hris-2/Crown_Keyboard/Ergogen/Outputs/left_stilts.dxf

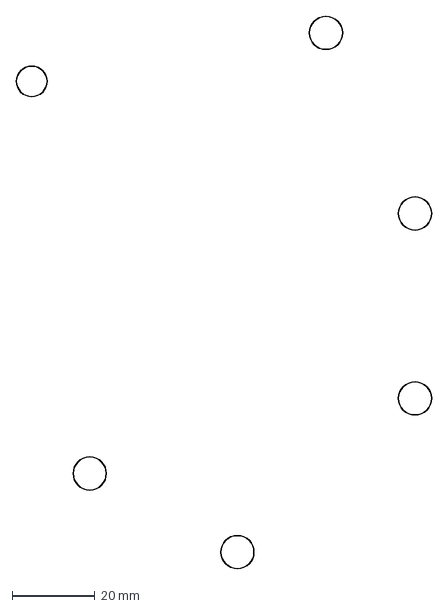
[picture p16: CAD file, 2025-05-29]
Ergogen/Outputs/left_stilts.dxf
100.2 x 133.3 mm
