hris-2/Crown_Keyboard/Ergogen/Outputs/Outlines/left_xlboard.dxf

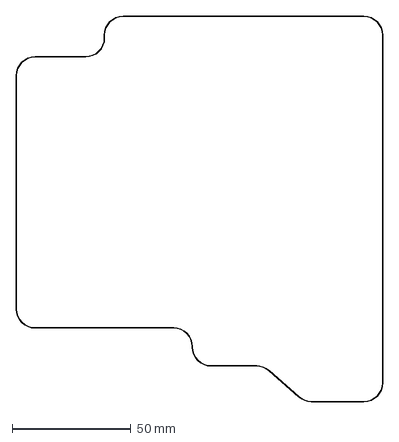
[picture p17: CAD file, 2025-05-29]
Ergogen/Outputs/Outlines/left_xlboard.dxf
154.0 x 162.0 mm
