hris-2/Crown_Keyboard/Ergogen/Outputs/left_mounting_holes.dxf

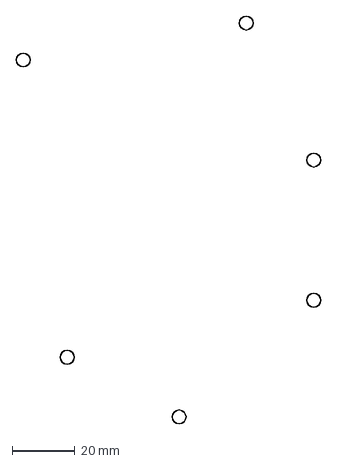
[picture p19: CAD file, 2025-05-29]
Ergogen/Outputs/left_mounting_holes.dxf
96.9 x 129.7 mm
