hris-2/Crown_Keyboard/Ergogen/Outputs/Outlines/left_niceview_template.dxf

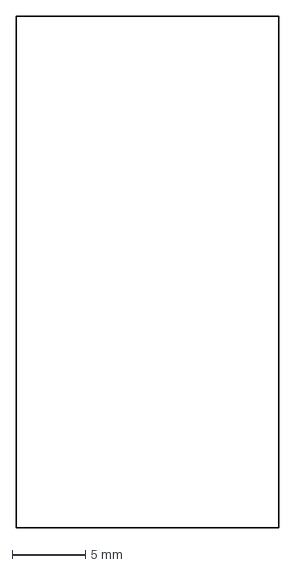
[picture p20: CAD file, 2025-05-29]
Ergogen/Outputs/Outlines/left_niceview_template.dxf
18.0 x 35.0 mm
