hris-2/Crown_Keyboard/Ergogen/Outputs/Unimportant/left_stilts-bottom_middle.dxf

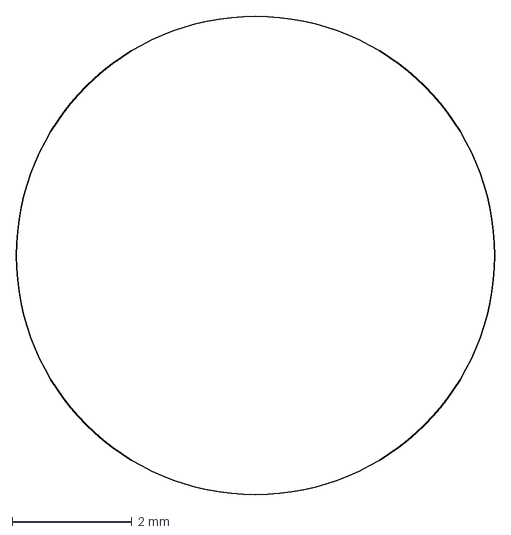
[picture p21: CAD file, 2025-05-29]
Ergogen/Outputs/Unimportant/left_stilts-bottom_middle.dxf
8.00 x 8.00 mm
