hris-2/Crown_Keyboard/Ergogen/Outputs/Outlines/left_stilts_w_holes.dxf

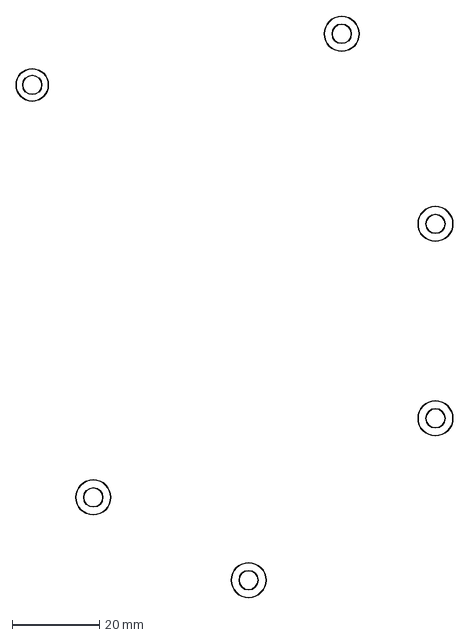
[picture p22: CAD file, 2025-05-29]
Ergogen/Outputs/Outlines/left_stilts_w_holes.dxf
100.2 x 133.3 mm
