hris-2/Crown_Keyboard/Ergogen/Outputs/right_pcb.dxf

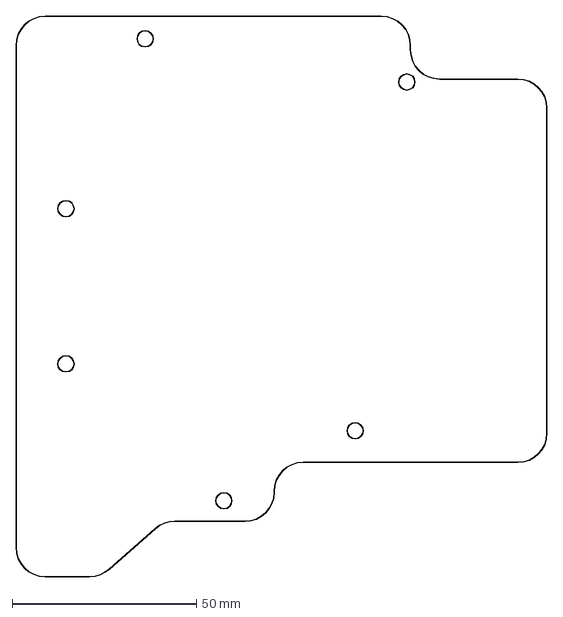
[picture p23: CAD file, 2025-05-29]
Ergogen/Outputs/right_pcb.dxf
144.0 x 152.0 mm
