hris-2/Crown_Keyboard/Ergogen/Outputs/both_combo.dxf

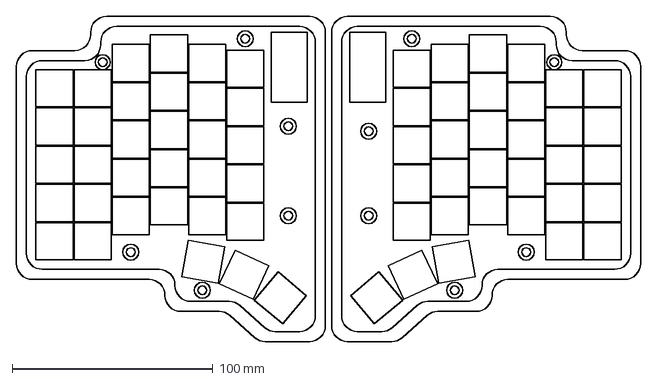
[picture p25: CAD file, 2025-05-29]
Ergogen/Outputs/both_combo.dxf
311.0 x 162.0 mm
