hris-2/Crown_Keyboard/Ergogen/Outputs/Outlines/left_stilts.dxf

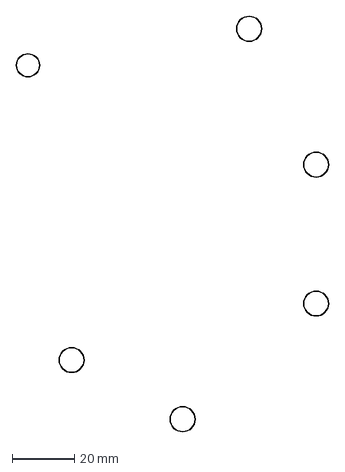
[picture p26: CAD file, 2025-05-29]
Ergogen/Outputs/Outlines/left_stilts.dxf
100.2 x 133.3 mm
