hris-2/Crown_Keyboard/Ergogen/Outputs/Unimportant/right_mounting_hole-bottom_left.dxf

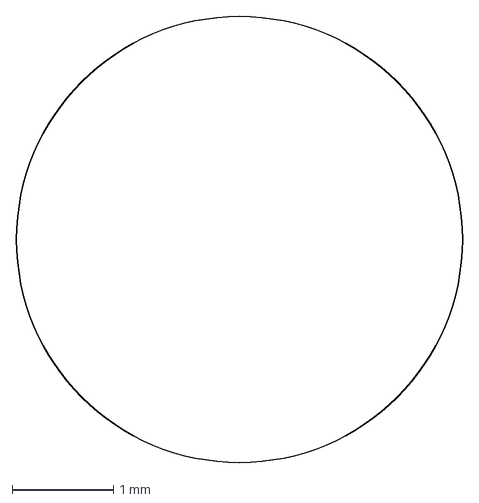
[picture p27: CAD file, 2025-05-29]
Ergogen/Outputs/Unimportant/right_mounting_hole-bottom_left.dxf
4.40 x 4.40 mm
