hris-2/Crown_Keyboard/Ergogen/Outputs/Outlines/left_mounting_holes.dxf

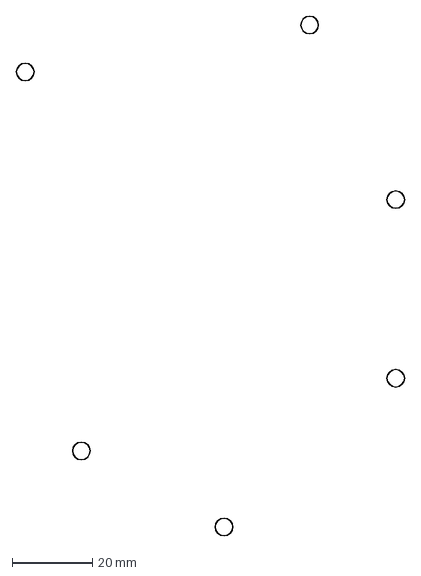
[picture p28: CAD file, 2025-05-29]
Ergogen/Outputs/Outlines/left_mounting_holes.dxf
96.9 x 129.7 mm
