hris-2/Crown_Keyboard/Ergogen/Outputs/left_pcb.dxf

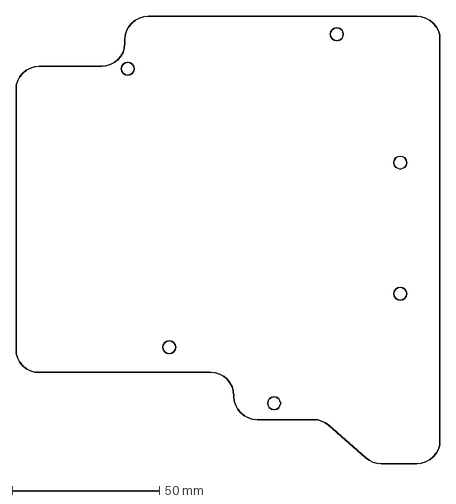
[picture p31: CAD file, 2025-05-29]
Ergogen/Outputs/left_pcb.dxf
144.0 x 152.0 mm
