hris-2/Crown_Keyboard/Ergogen/Outputs/Outlines/right_stilts.dxf

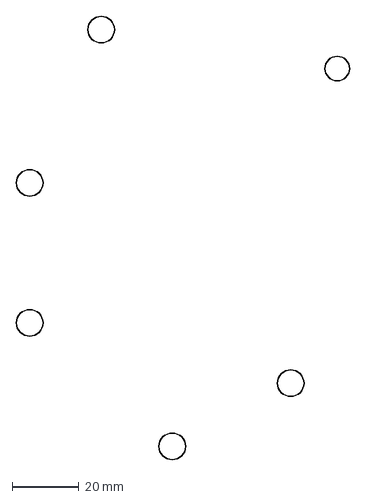
[picture p32: CAD file, 2025-05-29]
Ergogen/Outputs/Outlines/right_stilts.dxf
100.2 x 133.3 mm
