hris-2/Crown_Keyboard/Ergogen/Outputs/Unimportant/left_mounting_hole-bottom_middle.dxf

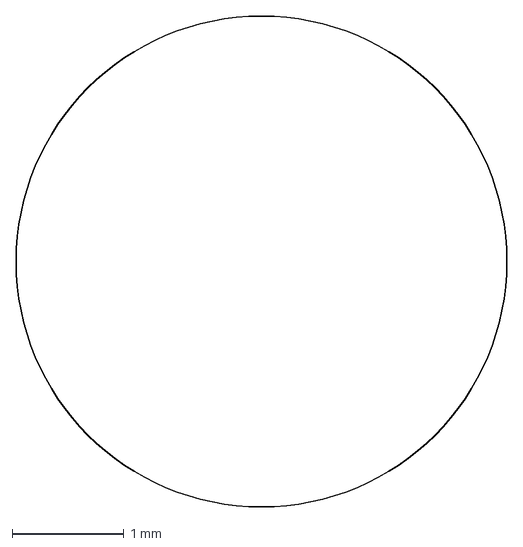
[picture p33: CAD file, 2025-05-29]
Ergogen/Outputs/Unimportant/left_mounting_hole-bottom_middle.dxf
4.40 x 4.40 mm
