hris-2/Crown_Keyboard/Ergogen/Outputs/left_board.dxf

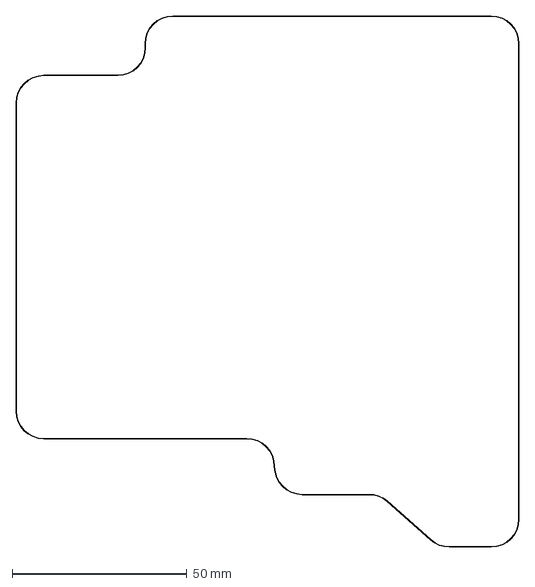
[picture p34: CAD file, 2025-05-29]
Ergogen/Outputs/left_board.dxf
144.0 x 152.0 mm
