hris-2/Crown_Keyboard/Ergogen/Outputs/Outlines/right_stlits_w_holes.dxf

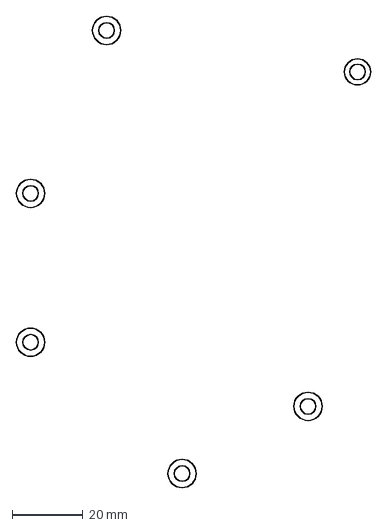
[picture p35: CAD file, 2025-05-29]
Ergogen/Outputs/Outlines/right_stlits_w_holes.dxf
100.2 x 133.3 mm
