hris-2/Crown_Keyboard/Ergogen/Outputs/Unimportant/left_stilts-top_right.dxf

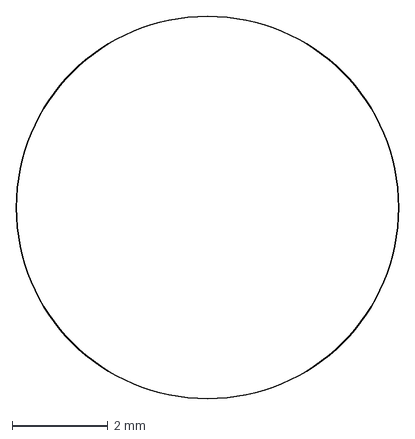
[picture p36: CAD file, 2025-05-29]
Ergogen/Outputs/Unimportant/left_stilts-top_right.dxf
8.00 x 8.00 mm
