hris-2/Crown_Keyboard/Ergogen/Outputs/left_niceview_template.dxf

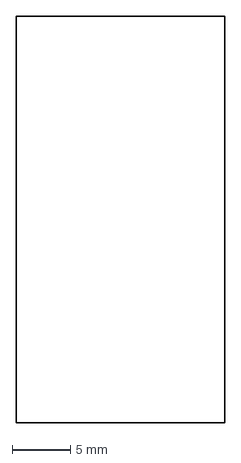
[picture p37: CAD file, 2025-05-29]
Ergogen/Outputs/left_niceview_template.dxf
18.0 x 35.0 mm
