hris-2/Crown_Keyboard/Ergogen/Outputs/Outlines/right_xlboard.dxf

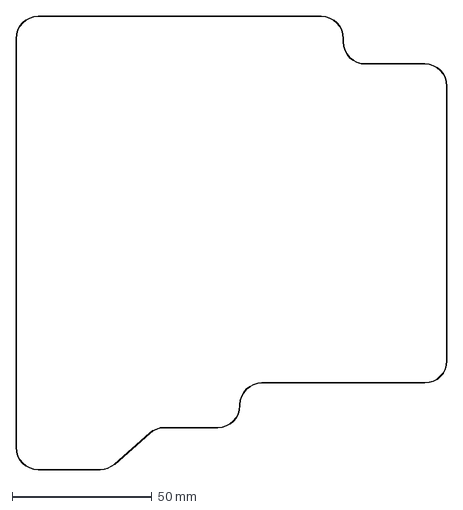
[picture p38: CAD file, 2025-05-29]
Ergogen/Outputs/Outlines/right_xlboard.dxf
154.0 x 162.0 mm
