hris-2/Crown_Keyboard/Ergogen/Outputs/Unimportant/right_stilts-bottom_middle.dxf

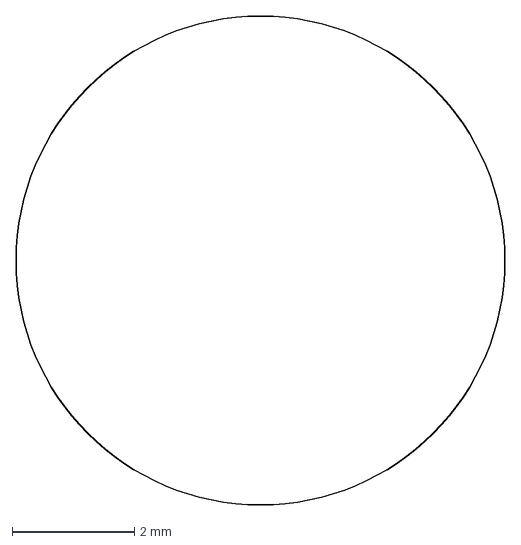
[picture p39: CAD file, 2025-05-29]
Ergogen/Outputs/Unimportant/right_stilts-bottom_middle.dxf
8.00 x 8.00 mm
