hris-2/Crown_Keyboard/Ergogen/Outputs/Outlines/left_pcb.dxf

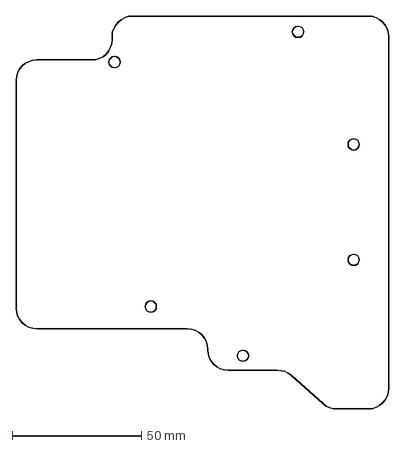
[picture p40: CAD file, 2025-05-29]
Ergogen/Outputs/Outlines/left_pcb.dxf
144.0 x 152.0 mm
