hris-2/Crown_Keyboard/Ergogen/Outputs/right_board.dxf

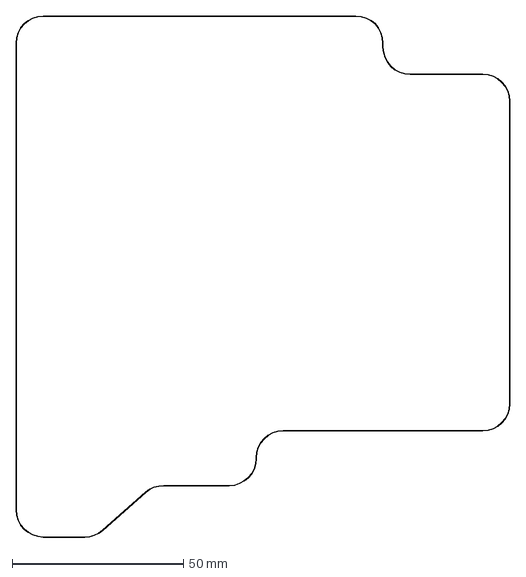
[picture p41: CAD file, 2025-05-29]
Ergogen/Outputs/right_board.dxf
144.0 x 152.0 mm
