hris-2/Crown_Keyboard/Ergogen/Outputs/left_xlboard.dxf

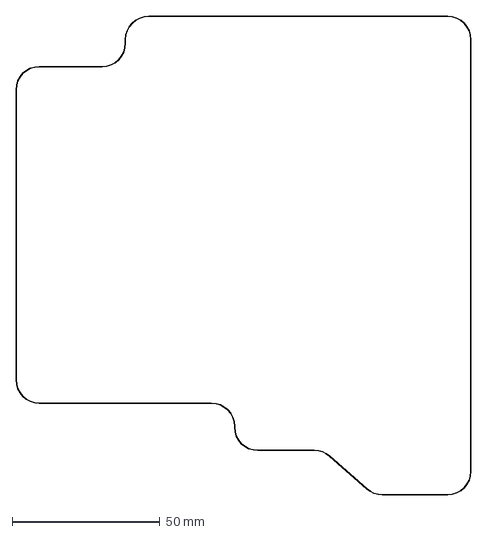
[picture p43: CAD file, 2025-05-29]
Ergogen/Outputs/left_xlboard.dxf
154.0 x 162.0 mm
