hris-2/Crown_Keyboard/Ergogen/Outputs/right_niceview_template.dxf

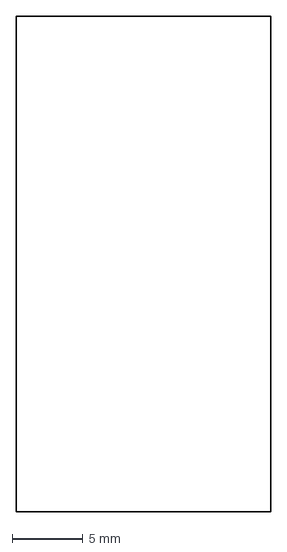
[picture p47: CAD file, 2025-05-29]
Ergogen/Outputs/right_niceview_template.dxf
18.0 x 35.0 mm
