hris-2/Crown_Keyboard/Ergogen/Outputs/Unimportant/left_stilts-top_left.dxf

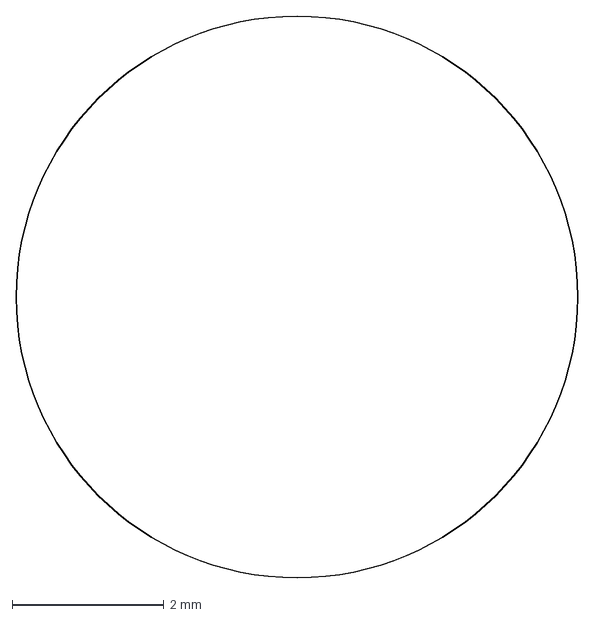
[picture p48: CAD file, 2025-05-29]
Ergogen/Outputs/Unimportant/left_stilts-top_left.dxf
7.40 x 7.40 mm
