hris-2/Crown_Keyboard/Ergogen/Outputs/Outlines/both_combo.dxf

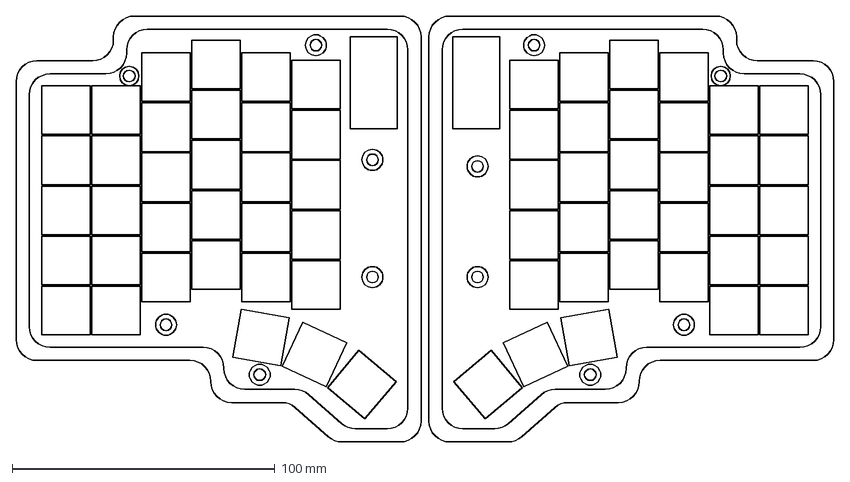
[picture p49: CAD file, 2025-05-29]
Ergogen/Outputs/Outlines/both_combo.dxf
311.0 x 162.0 mm
