hris-2/Crown_Keyboard/Ergogen/Outputs/Unimportant/right_stilts-bottom_left.dxf

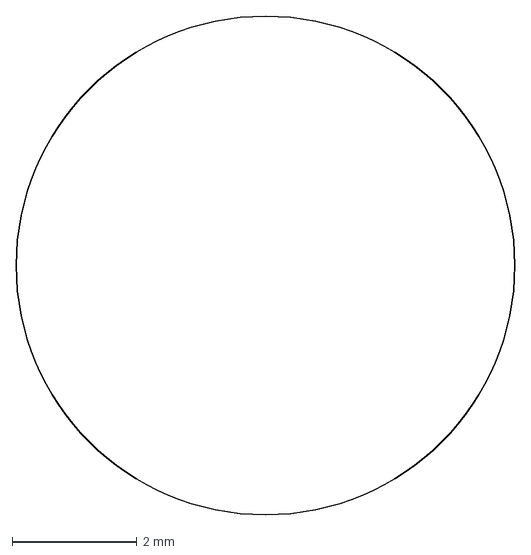
[picture p50: CAD file, 2025-05-29]
Ergogen/Outputs/Unimportant/right_stilts-bottom_left.dxf
8.00 x 8.00 mm
