hris-2/Crown_Keyboard/Ergogen/Outputs/Outlines/raw.dxf

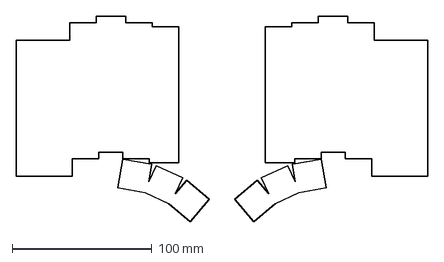
[picture p51: CAD file, 2025-05-29]
Ergogen/Outputs/Outlines/raw.dxf
294.0 x 147.0 mm
