hris-2/Crown_Keyboard/Ergogen/Outputs/Unimportant/right_stilts-top_right.dxf

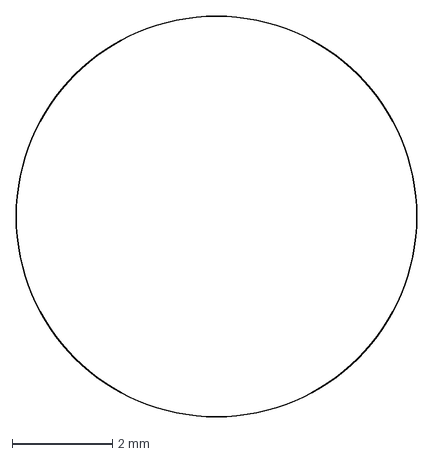
[picture p52: CAD file, 2025-05-29]
Ergogen/Outputs/Unimportant/right_stilts-top_right.dxf
8.00 x 8.00 mm
