hris-2/Crown_Keyboard/Ergogen/Outputs/Outlines/right_keys.dxf

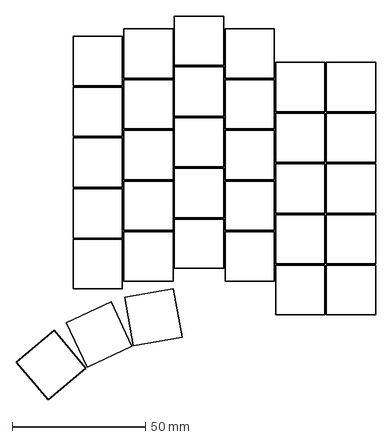
[picture p53: CAD file, 2025-05-29]
Ergogen/Outputs/Outlines/right_keys.dxf
134.8 x 144.0 mm
