hris-2/Crown_Keyboard/Ergogen/Outputs/Outlines/left_keys.dxf

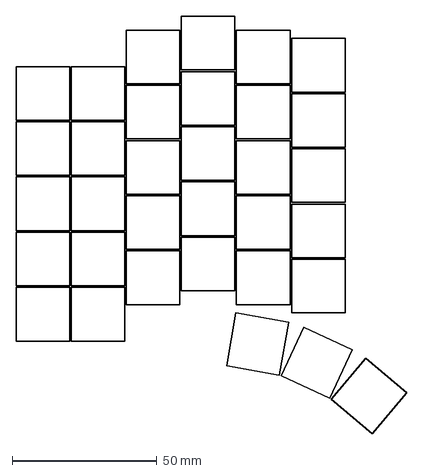
[picture p55: CAD file, 2025-05-29]
Ergogen/Outputs/Outlines/left_keys.dxf
134.8 x 144.0 mm
