hris-2/Crown_Keyboard/Ergogen/Outputs/Outlines/keys_all.dxf

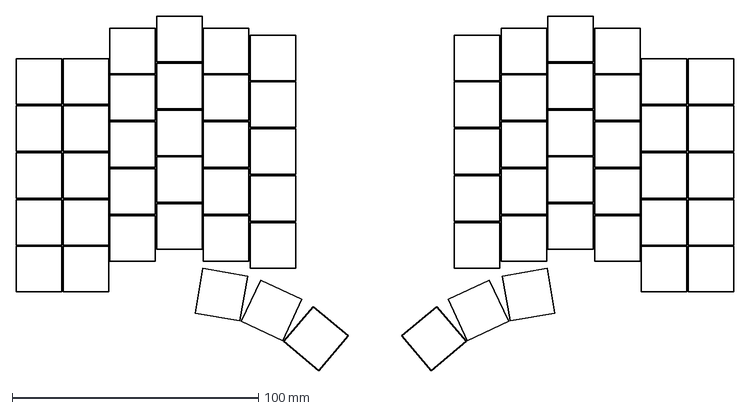
[picture p57: CAD file, 2025-05-29]
Ergogen/Outputs/Outlines/keys_all.dxf
291.5 x 144.0 mm
