hris-2/Crown_Keyboard/Ergogen/Outputs/Unimportant/left_stilts-top_middle.dxf

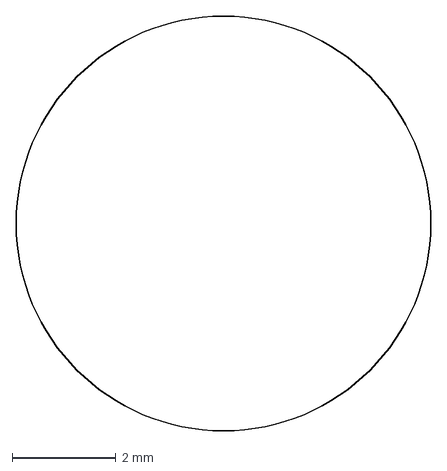
[picture p58: CAD file, 2025-05-29]
Ergogen/Outputs/Unimportant/left_stilts-top_middle.dxf
8.00 x 8.00 mm
