hris-2/Crown_Keyboard/Ergogen/Outputs/Outlines/demo.dxf

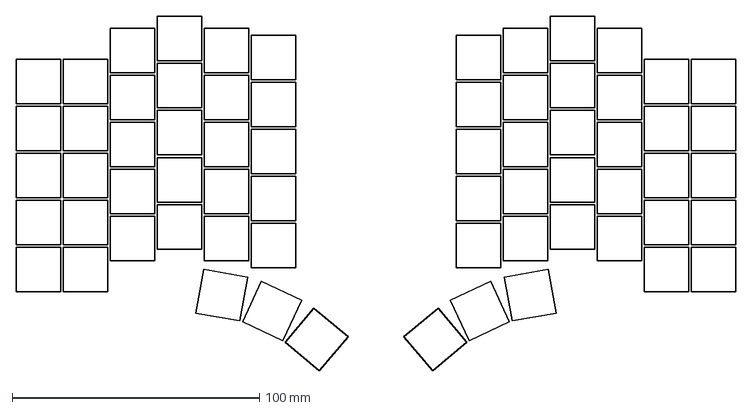
[picture p59: CAD file, 2025-05-29]
Ergogen/Outputs/Outlines/demo.dxf
291.0 x 143.4 mm
