hris-2/Crown_Keyboard/Ergogen/Outputs/Unimportant/left_stilts-bottom_left.dxf

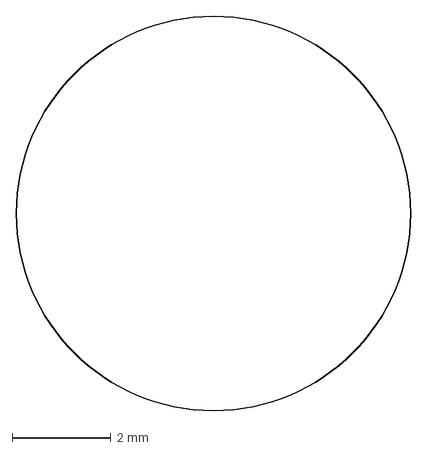
[picture p60: CAD file, 2025-05-29]
Ergogen/Outputs/Unimportant/left_stilts-bottom_left.dxf
8.00 x 8.00 mm
