hris-2/Crown_Keyboard/Ergogen/Outputs/Unimportant/right_mounting_hole-top_left.dxf

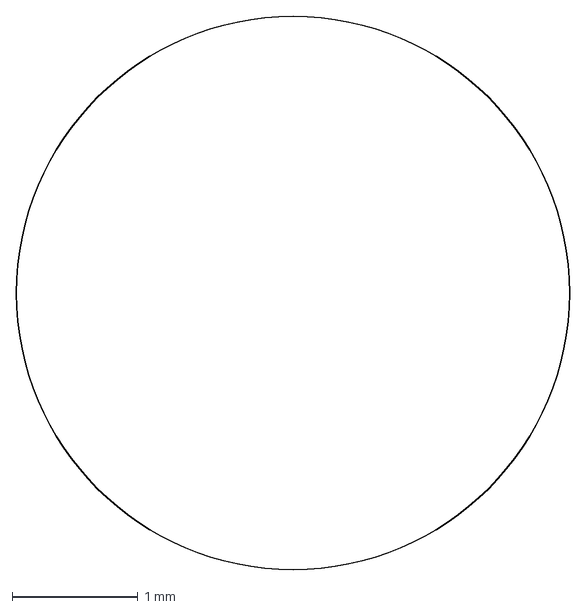
[picture p61: CAD file, 2025-05-29]
Ergogen/Outputs/Unimportant/right_mounting_hole-top_left.dxf
4.40 x 4.40 mm
