hris-2/Crown_Keyboard/Ergogen/Outputs/Unimportant/raw.dxf

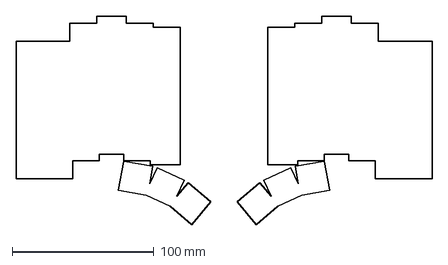
[picture p63: CAD file, 2025-05-29]
Ergogen/Outputs/Unimportant/raw.dxf
294.0 x 147.0 mm
