hris-2/Crown_Keyboard/Ergogen/Outputs/Unimportant/left_keys.dxf

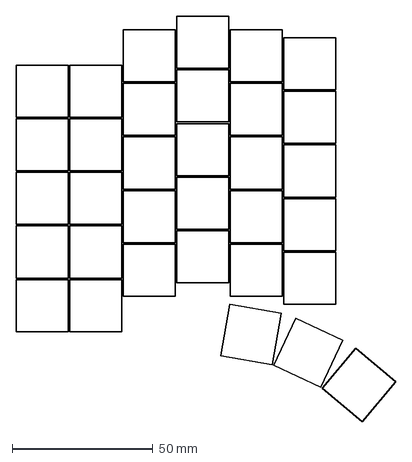
[picture p64: CAD file, 2025-05-29]
Ergogen/Outputs/Unimportant/left_keys.dxf
134.8 x 144.0 mm
