hris-2/Crown_Keyboard/Ergogen/Outputs/Unimportant/demo.dxf

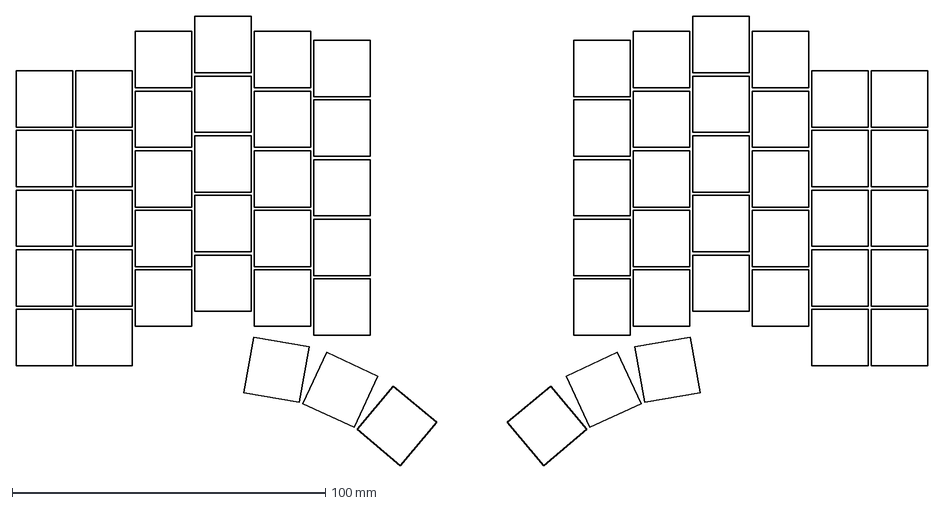
[picture p65: CAD file, 2025-05-29]
Ergogen/Outputs/Unimportant/demo.dxf
291.0 x 143.4 mm
