hris-2/Crown_Keyboard/Ergogen/Outputs/Unimportant/keys_all.dxf

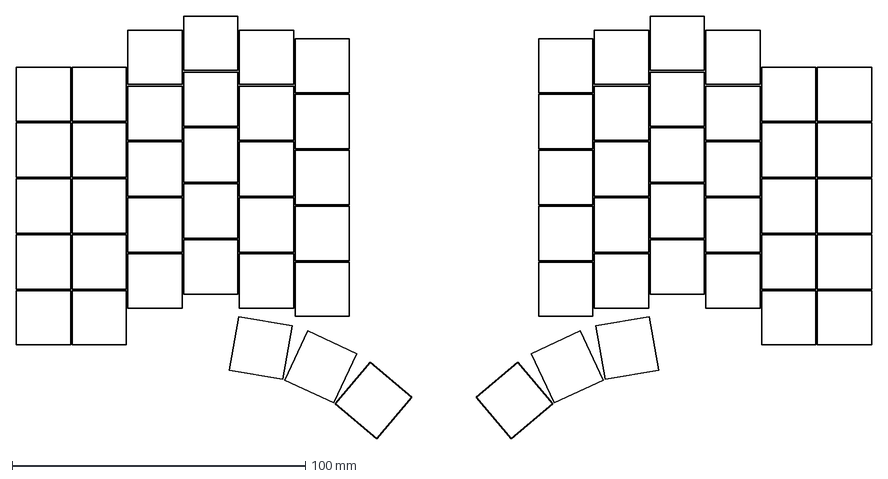
[picture p66: CAD file, 2025-05-29]
Ergogen/Outputs/Unimportant/keys_all.dxf
291.5 x 144.0 mm
